hanyuz77/Techin-514-Final-Project/TECHIN514_w26_project_PCB/PCB LAB.kicad_sch

## KiCad design TECHIN514_w26_project_PCB/PCB LAB.kicad_sch (2026-01-30)

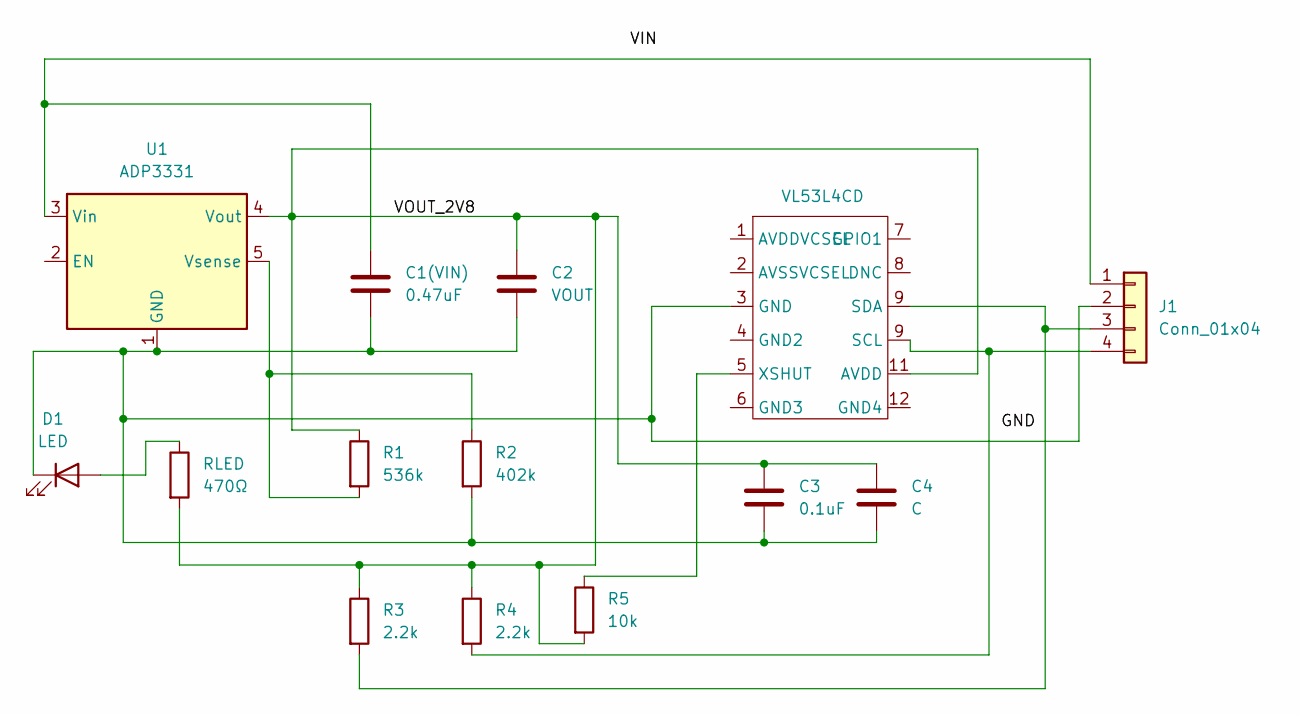
[picture p10: schematic PCB LAB.kicad_sch]

Parts:
C1(VIN): 0.47uF
C2: VOUT
C3: 0.1uF
C4: C
D1: LED
J1: Conn_01x04
R1: 536k
R2: 402k
R3, R4: 2.2k
R5: 10k
RLED: 470Ω
U1: ADP3331; DFN-6-1EP_3x3mm_P0.95mm_EP1.7x2.6mm
VL53L4CD: (no value)

Connections:
unnamed: C1(VIN).1, J1.1, U1.3 (Vin)
unnamed: C1(VIN).2, C2.2, C3.2, C4.2, D1.1 (K), J1.2, R2.2, U1.1 (GND), U1.7 (GND), VL53L4CD.3 (GND)
unnamed: D1.2 (A), RLED.1
unnamed: J1.3 (SDA), R3.2, VL53L4CD.9 (SDA)
unnamed: J1.4 (SCL), R4.2, VL53L4CD.9 (SDA)
unnamed: R1.2, R2.1, U1.5 (Vsense)
unnamed: R5.1, VL53L4CD.5 (XSHUT)
VOUT_2V8: C2.1, C3.1, C4.1, R1.1, R3.1, R4.1, R5.2, RLED.2, U1.4 (Vout), VL53L4CD.11 (AVDD)
